pienjo/ClockRadio/Timefuncs.c

/*
Copyright 2018, Martijn van Buul <martijn.van.buul@gmail.com>

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
THE SOFTWARE IS PROVIDED "AS IS" AND THE AUTHOR DISCLAIMS ALL WARRANTIES WITH
REGARD TO THIS SOFTWARE INCLUDING ALL IMPLIED WARRANTIES OF MERCHANTABILITY AND
FITNESS. IN NO EVENT SHALL THE AUTHOR BE LIABLE FOR ANY SPECIAL, DIRECT,
INDIRECT, OR CONSEQUENTIAL DAMAGES OR ANY DAMAGES WHATSOEVER RESULTING FROM
LOSS OF USE, DATA OR PROFITS, WHETHER IN AN ACTION OF CONTRACT, NEGLIGENCE OR
OTHER TORTIOUS ACTION, ARISING OUT OF OR IN CONNECTION WITH THE USE OR
PERFORMANCE OF THIS SOFTWARE.
*/
#include "Timefuncs.h"
#include "BCDFuncs.h"
#include "DateTime.h"
#include <avr/pgmspace.h>
#include <stdbool.h>

const uint8_t PROGMEM dpm[] =
{
  0x31, // jan
  0x28, // feb
  0x31, // mar
  0x30, // apr
  0x31, // may
  0x30, // jun
  0x31, // jul
  0x31, // aug
  0x30, // sep
  0x31, // oct
  0x30, // nov
  0x31, // dec;
};

uint8_t GetDaysPerMonth(const uint8_t Month, const uint8_t Year)
{
  uint8_t days = pgm_read_byte(dpm + BCDToBin(Month) - 1);
  //uint8_t year_dec = 10 * (year >> 4) + (year & 0xf);
  if (Month == 2 && (Year %4 == 0))
    days++; // February on a leap year, no need to fix BCD.
  
  return days;
}

const uint8_t PROGMEM dowTable[] = { 0,3,2,5,0,3,5,1,4,6,2,4 };

uint8_t GetDayOfWeek(uint8_t Day, uint8_t Month, uint8_t year /* 20xx */) // 1 - monday
{
  year = BCDToBin(year);
  year -= ( Month < 3);
  
  return  ((year + year / 4 /* -y/100 + y / 400 */ + pgm_read_byte(dowTable + BCDToBin(Month) -1) + BCDToBin(Day) - 1) % 7) + 1;
}

void NormalizeHours(struct DateTime *timestamp)
{
  if (timestamp->hour < 0x24)
    return; // Nothing to do.
  
  if (timestamp->hour > 0x50)
  {
    // Underflow
    timestamp->day = BCDSub(timestamp->day, 0x1); 
    
    --timestamp->wday;
    if (timestamp->wday == 0)
      timestamp->wday = 7;
      
    timestamp->hour = BCDAdd(timestamp->hour, 0x24);
  }  
  
  if(timestamp->hour >= 0x24)
  {
    timestamp->day = BCDAdd(timestamp->day, 0x01);
    timestamp->wday ++;
    if (timestamp->wday == 8)
      timestamp->wday = 1;
      
    timestamp->hour = BCDSub(timestamp->hour, 0x24); 
  }
  
  if ((timestamp->day == 0) || (timestamp->day > 0x50))
  {
    timestamp->month = BCDSub(timestamp->month, 1); 
    if (timestamp->month == 0)
    {
      timestamp->year = BCDSub(timestamp->year, 1); 
      timestamp->month = 0x12;
    }
    
    timestamp->day = BCDAdd( GetDaysPerMonth(timestamp->month, timestamp->year), timestamp->day);
    return;
  }
  
  uint8_t daysThisMonth = GetDaysPerMonth(timestamp->month, timestamp->year);
 
  if (daysThisMonth < timestamp->day)
  {
    timestamp->month = BCDAdd(timestamp->month, 1);
    timestamp->day = BCDSub(timestamp->day, daysThisMonth);
    if (timestamp->month == 0x13)
    {
      timestamp->year = BCDAdd(timestamp->year, 1);      
      timestamp->month = 1;
    }
  }
}

uint8_t GetDateOfLastSunday(uint8_t month, uint8_t year) 
{
  const uint8_t lastDayOfMonth = GetDaysPerMonth(month, year);
  // Determine the day-of-week of that date. If it is a sunday, then that's the answer.
  
  const uint8_t weekdayOfLastDay = GetDayOfWeek(lastDayOfMonth, month, year);
  
  if (weekdayOfLastDay == 7)
  {
    return lastDayOfMonth;
  }
  
  // If it is monday(1), then the transition is on the previous day. If it was on tuesday(2), it was two days before, etc.
  return BCDSub(lastDayOfMonth, weekdayOfLastDay);
}

_Bool IsDSTActive(const struct DateTime *timestamp, _Bool timestampIsUTC)
{
  // DST is active from the last sunday of march until the last sunday of october. 
  if (timestamp->month < 3 || timestamp->month > 0x10) // jan, feb, nov, dec
  {
    return false;
  } else if (timestamp->month > 3 && timestamp->month < 0x10) // apr, may, jun, jul, aug, sept
  {
    return true;
  }
  
  // march or october. Transition day is the last sunday of this month.
  const uint8_t transitionDay = GetDateOfLastSunday(timestamp->month, timestamp->year);
  _Bool pastTransitionDay;
  if (timestamp->day == transitionDay)
  {
    // Transition from CET to CEST is at 02:00 UTC+1, or at 1:00 UTC.
    // Transition from CEST to CET is at 03:00 UTC+2, or at 1:00 UTC.
    if (timestampIsUTC)
      pastTransitionDay = (timestamp->hour > 0);
    else
    {
      // 02:00 - 03:00 occurs twice in october. 
      // For the sake of simplicity, assume DST is no longer in effect when time is set after 02:00
      pastTransitionDay = (timestamp->hour >= 2); 
    }
  }
  else
  {
    pastTransitionDay = (timestamp->day > transitionDay);
  }
  
  return (timestamp->month == 3 ? pastTransitionDay : !pastTransitionDay);
}

void UTCToCentralEuropeanTime(struct DateTime *timestamp)
{
  if (IsDSTActive(timestamp, true))
    timestamp->hour = BCDAdd(timestamp->hour, 2);
  else
    timestamp->hour = BCDAdd(timestamp->hour, 1);
    
  NormalizeHours(timestamp);
}

void CentralEuropeanTimeToUTC(struct DateTime *timestamp)
{
  if (IsDSTActive(timestamp, false))
    timestamp->hour = BCDSub(timestamp->hour, 2);
  else
    timestamp->hour = BCDSub(timestamp->hour, 1);
    
  NormalizeHours(timestamp);
}

// Use a naive lookup table
const uint8_t PROGMEM DaylightTable[] =
{
  // Hour of rise, hour of set
  /* Jan */ 0x07,  0x18,
  /* Feb */ 0x07,  0x18,
  /* Mar */ 0x06,  0x19,
  /* Apr */ 0x06,  0x21,
  /* May */ 0x05,  0x22,
  /* Jun */ 0x05,  0x22,
  /* Jul */ 0x05,  0x22,
  /* Aug */ 0x05,  0x21,
  /* Sep */ 0x06,  0x20,
  /* Oct */ 0x06,  0x19,
  /* Nov */ 0x07,  0x18,
  /* Dec */ 0x07,  0x18,
};

_Bool ItIsDarkOutside(const struct DateTime *timestamp) 
{
  uint8_t idx = timestamp->month - 1;
  if (idx > 9) idx -= 6;
  idx += idx;
  
  if (timestamp->hour < pgm_read_byte(DaylightTable + idx))
    return 1;
  if (timestamp->hour >= pgm_read_byte(DaylightTable + idx + 1))
    return 1;
  return 0;
}
